ugokutennp/flow-eye/Rev1.1/PCB/Silk/P1.png

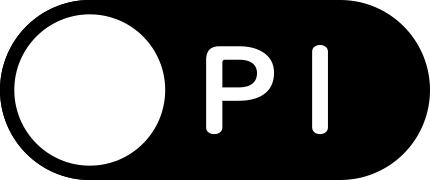
Rev1.1/PCB/Silk/P1.png
