ugokutennp/flow-eye/Rev1.1/PCB/Silk/P2.png

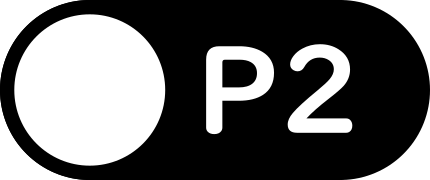
Rev1.1/PCB/Silk/P2.png
